kanawati975/Voron_Switchwire/Emergency Mount/Pictures/00.jpg

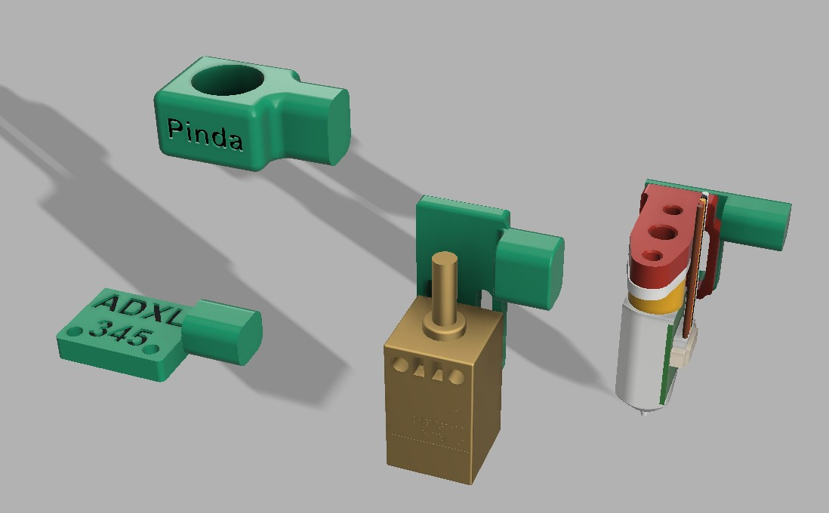
Emergency Mount/Pictures/00.jpg
