kanawati975/Voron_Switchwire/Emergency Mount/Pictures/1.jpg

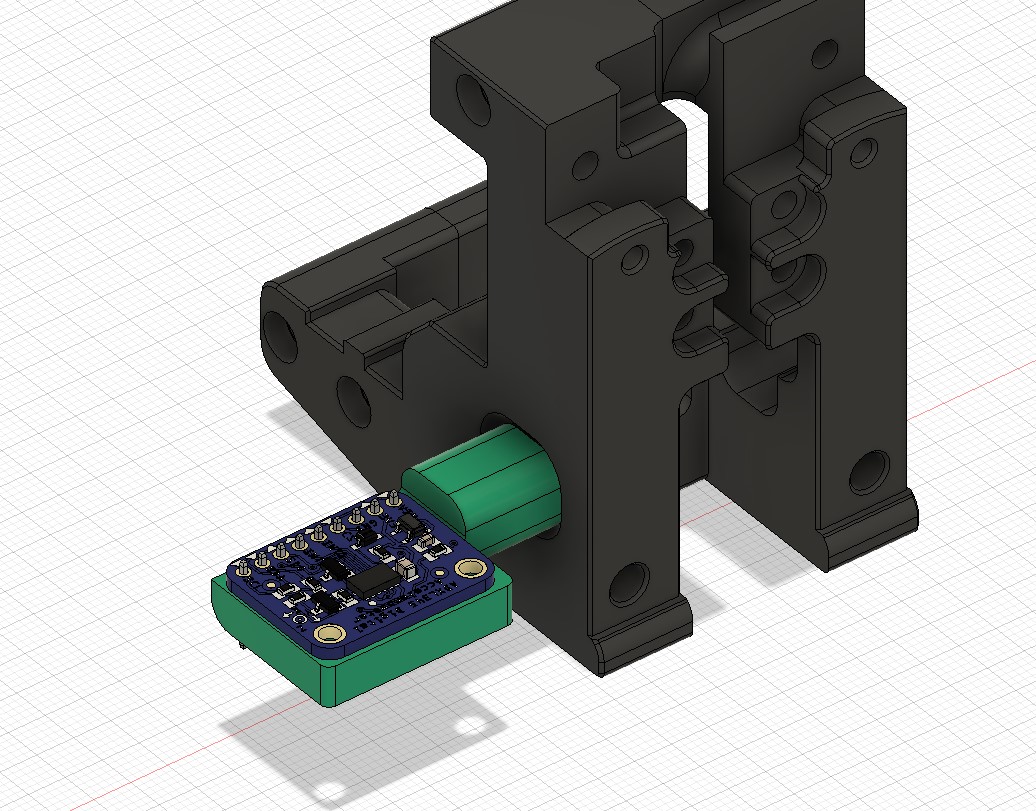
Emergency Mount/Pictures/1.jpg
