kanawati975/Voron_Switchwire/Emergency Mount/Pictures/2.jpeg

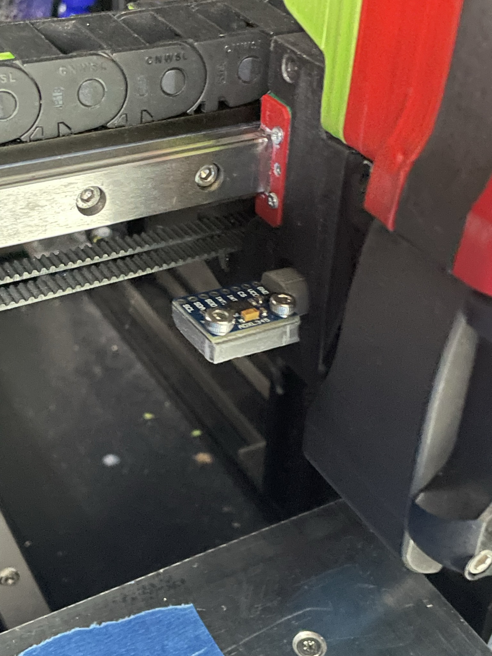
Emergency Mount/Pictures/2.jpeg
