kanawati975/Voron_Switchwire/Emergency Mount/Pictures/3.jpeg

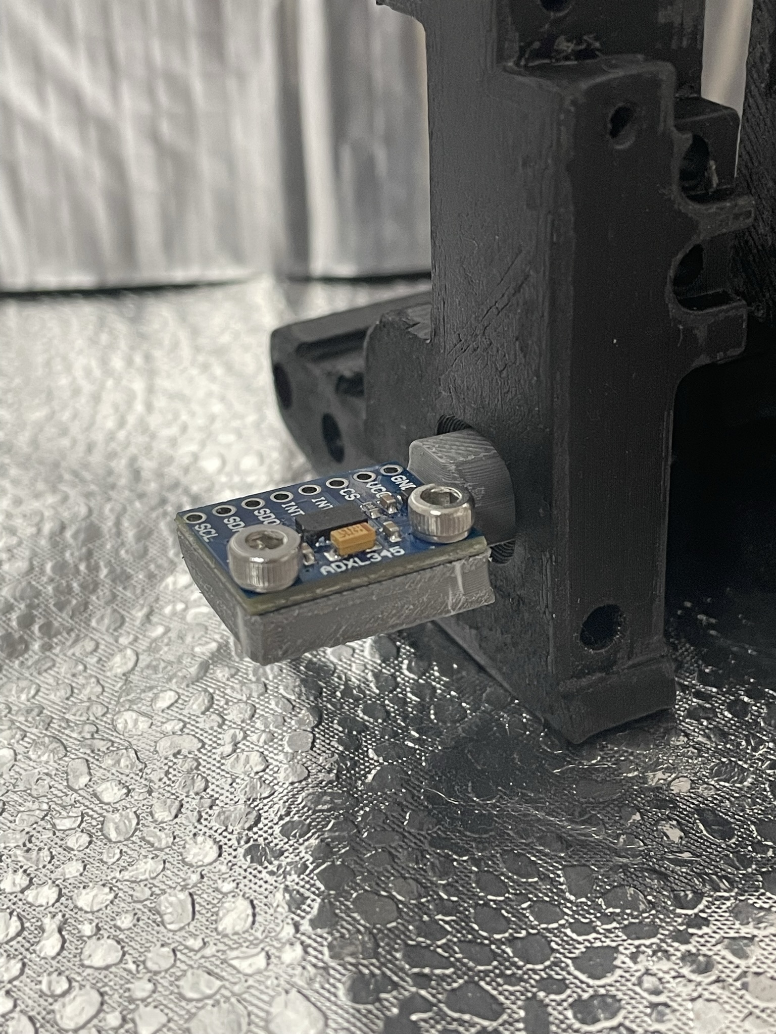
Emergency Mount/Pictures/3.jpeg
