kanawati975/Voron_Switchwire/Emergency Mount/Pictures/4.jpeg

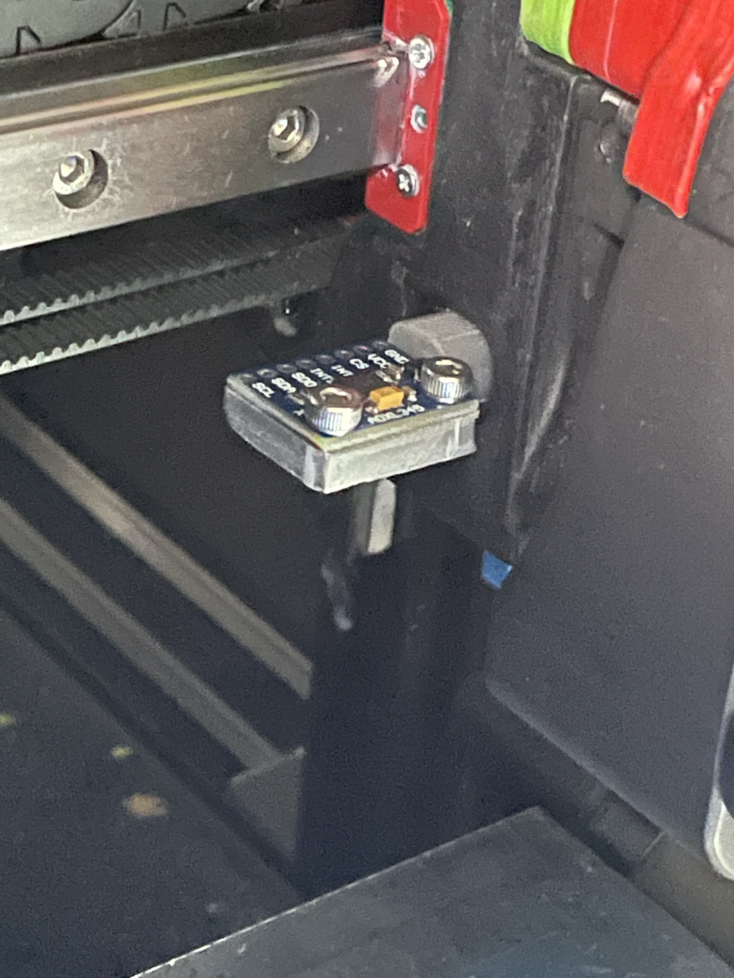
Emergency Mount/Pictures/4.jpeg
