kanawati975/Voron_Switchwire/Emergency Mount/Pictures/5.jpg

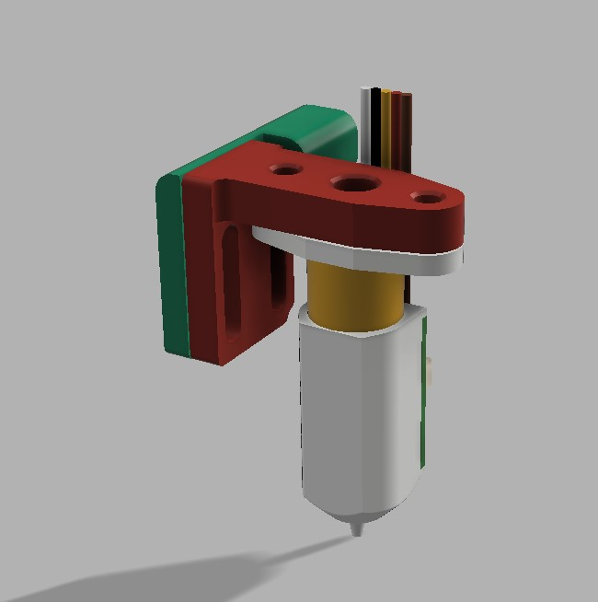
Emergency Mount/Pictures/5.jpg
