kanawati975/Voron_Switchwire/Emergency Mount/Pictures/6.jpeg

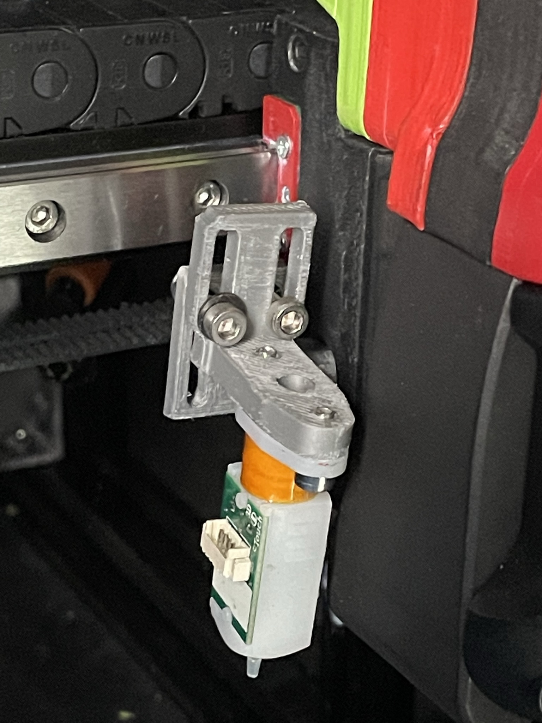
Emergency Mount/Pictures/6.jpeg
