kanawati975/Voron_Switchwire/Emergency Mount/Pictures/7.jpeg

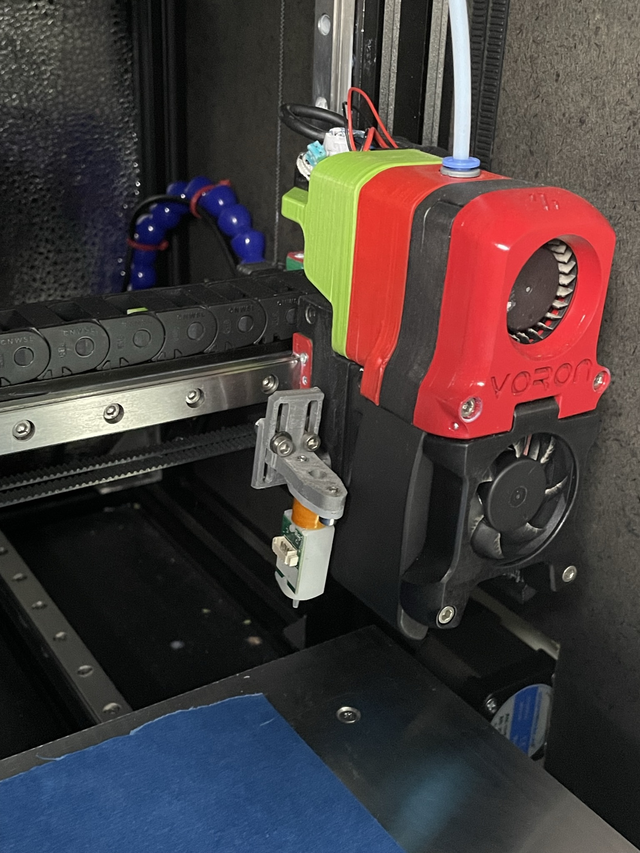
Emergency Mount/Pictures/7.jpeg
