kanawati975/Voron_Switchwire/Emergency Mount/Pictures/8.jpg

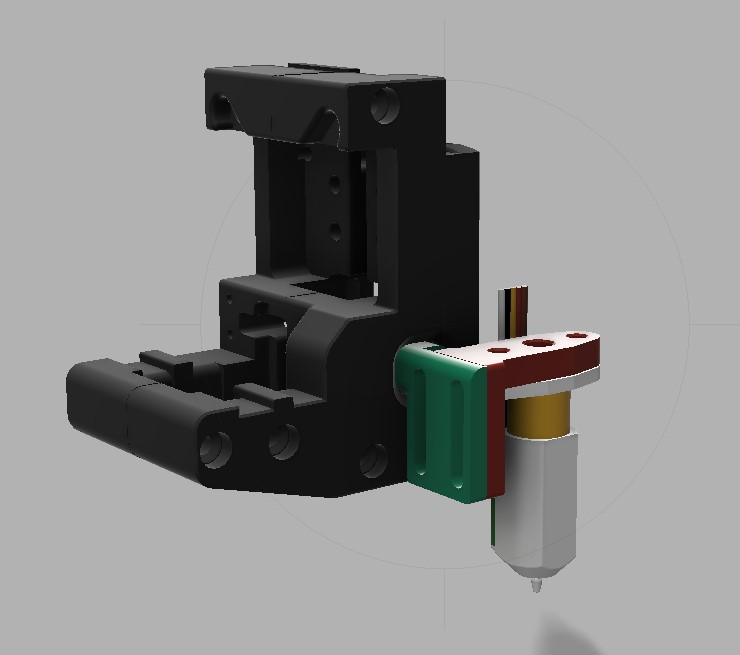
Emergency Mount/Pictures/8.jpg
