kanawati975/Voron_Switchwire/Emergency Mount/Pictures/9.jpg

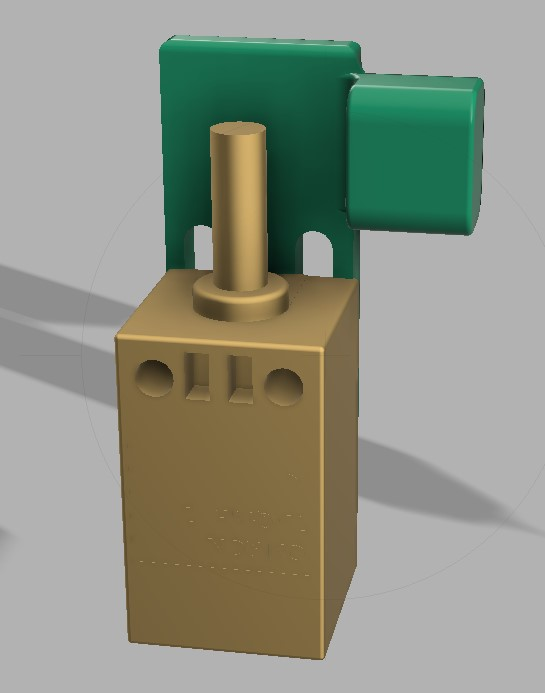
Emergency Mount/Pictures/9.jpg
