kanawati975/Voron_Switchwire/Images/IMG_6733.jpeg

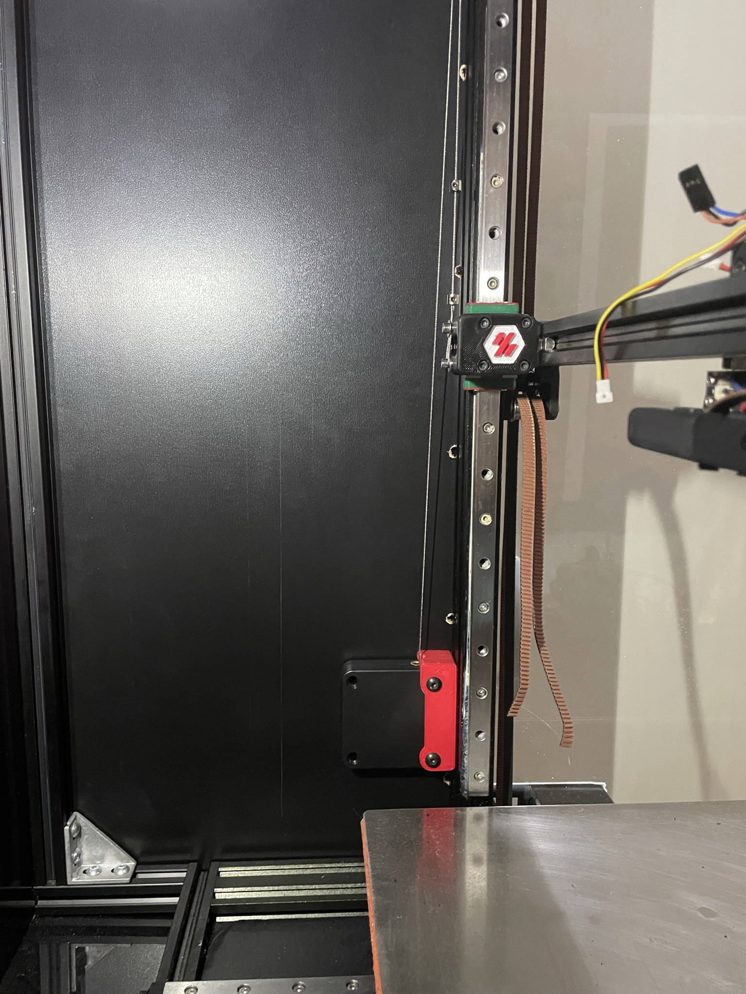
Images/IMG_6733.jpeg
