kanawati975/Voron_Switchwire/Images/IMG_6734.jpeg

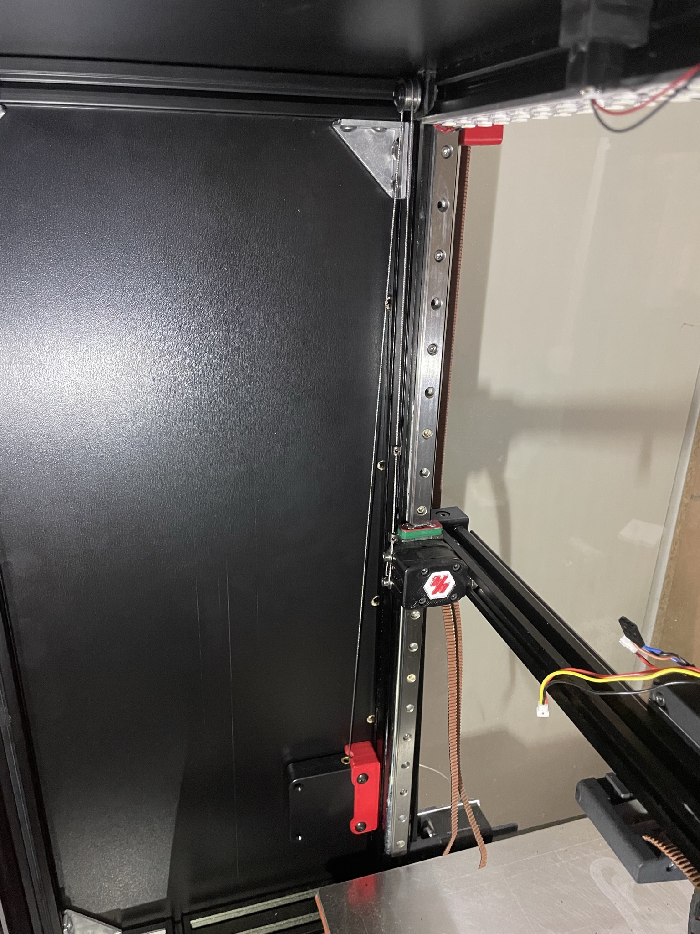
Images/IMG_6734.jpeg
