kanawati975/Voron_Switchwire/Images/IMG_6736.jpeg

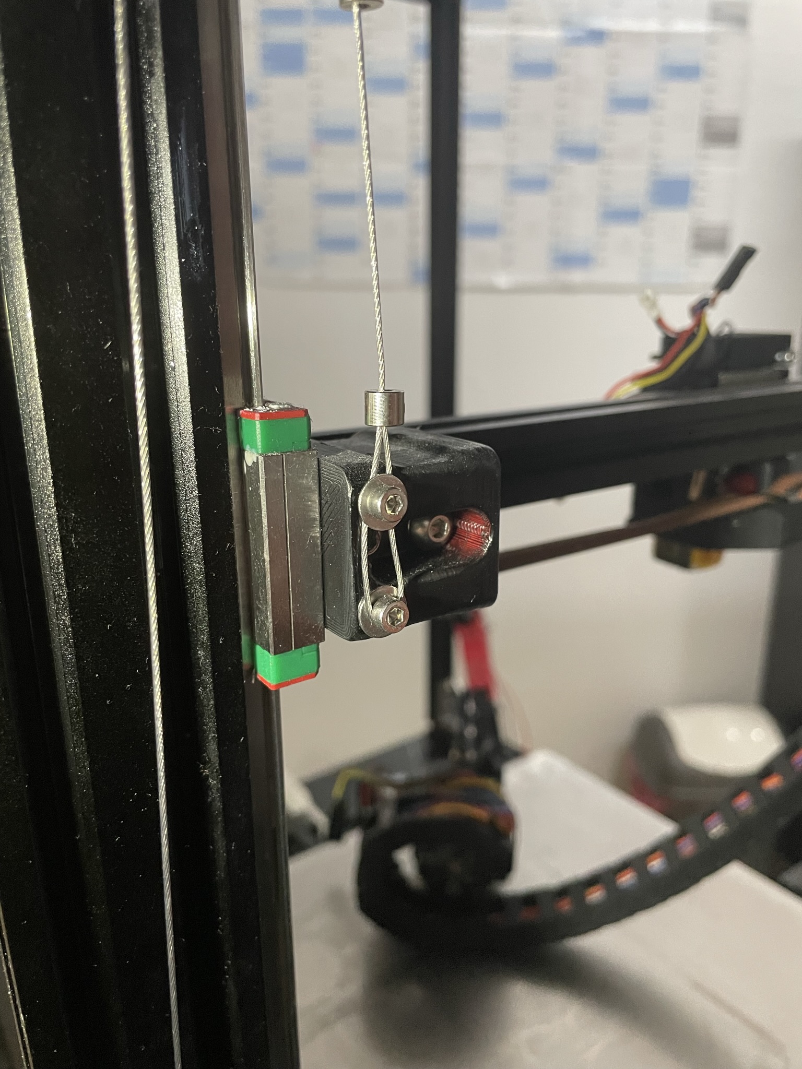
Images/IMG_6736.jpeg
