kanawati975/Voron_Switchwire/Images/IMG_6825.JPEG

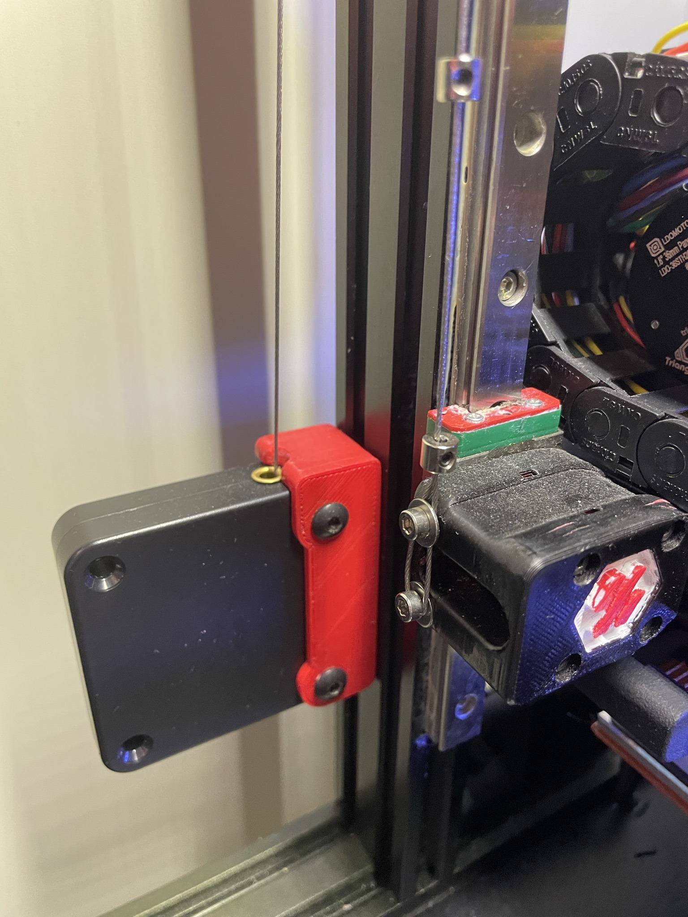
Images/IMG_6825.JPEG
