kanawati975/Voron_Switchwire/Images/IMG_6827.JPEG

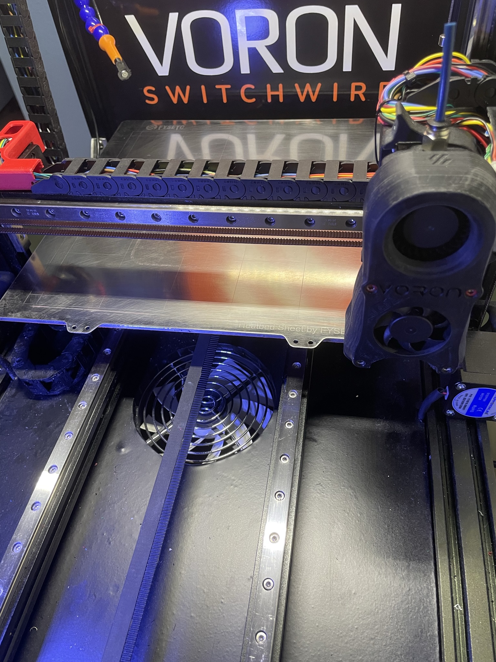
Images/IMG_6827.JPEG
