kanawati975/Voron_Switchwire/Images/IMG_6830.JPEG

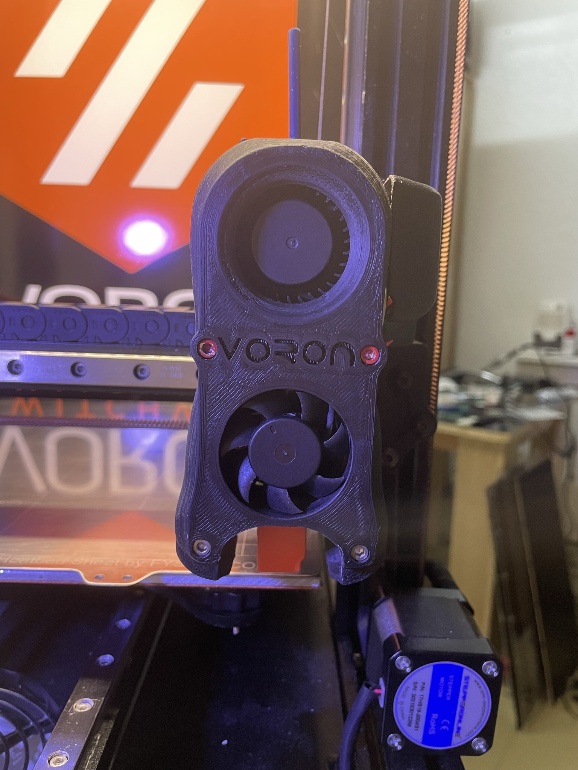
Images/IMG_6830.JPEG
