kanawati975/Voron_Switchwire/Images/IMG_6831.JPEG

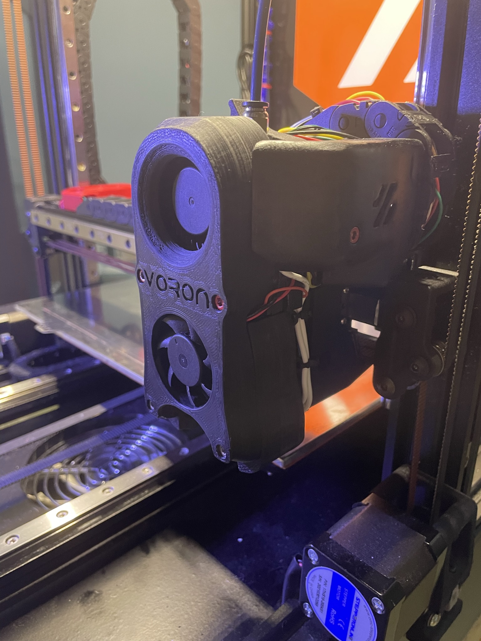
Images/IMG_6831.JPEG
