kanawati975/Voron_Switchwire/Images/IMG_6832.JPEG

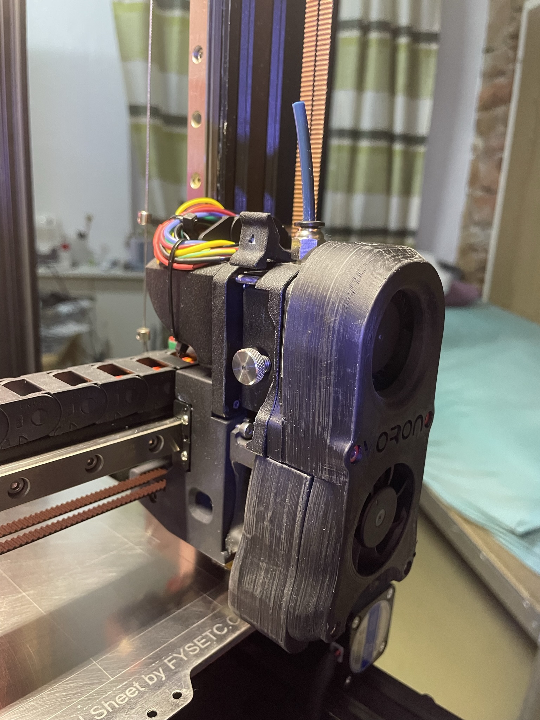
Images/IMG_6832.JPEG
