kanawati975/Voron_Switchwire/Images/IMG_6833.JPEG

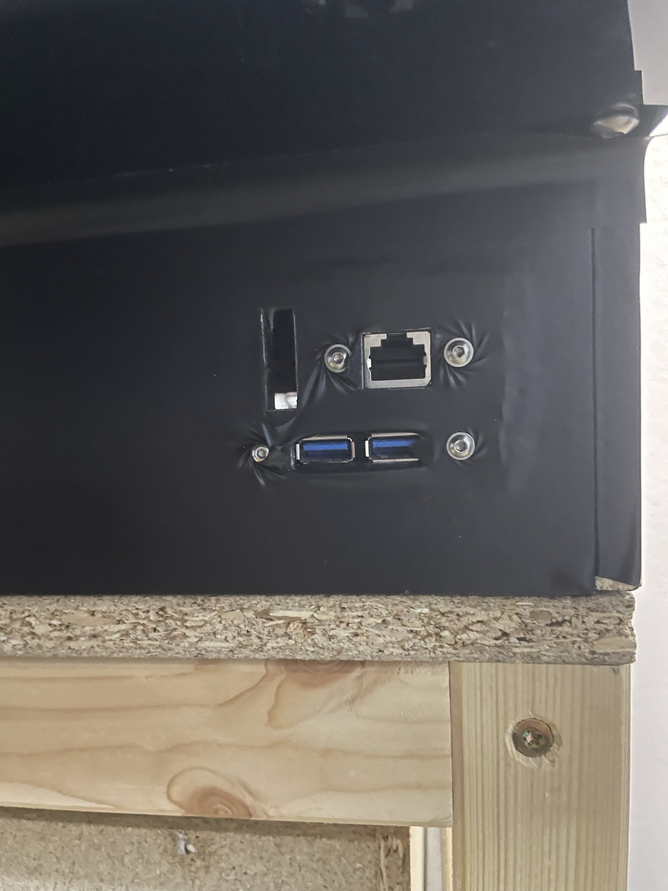
Images/IMG_6833.JPEG
