kanawati975/Voron_Switchwire/Images/IMG_6835.JPEG

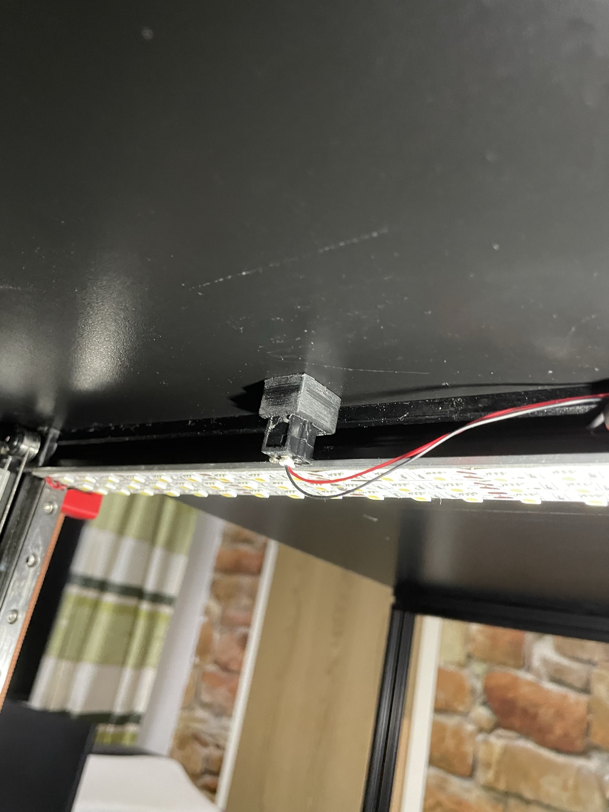
Images/IMG_6835.JPEG
