kanawati975/Voron_Switchwire/Images/IMG_6837.JPEG

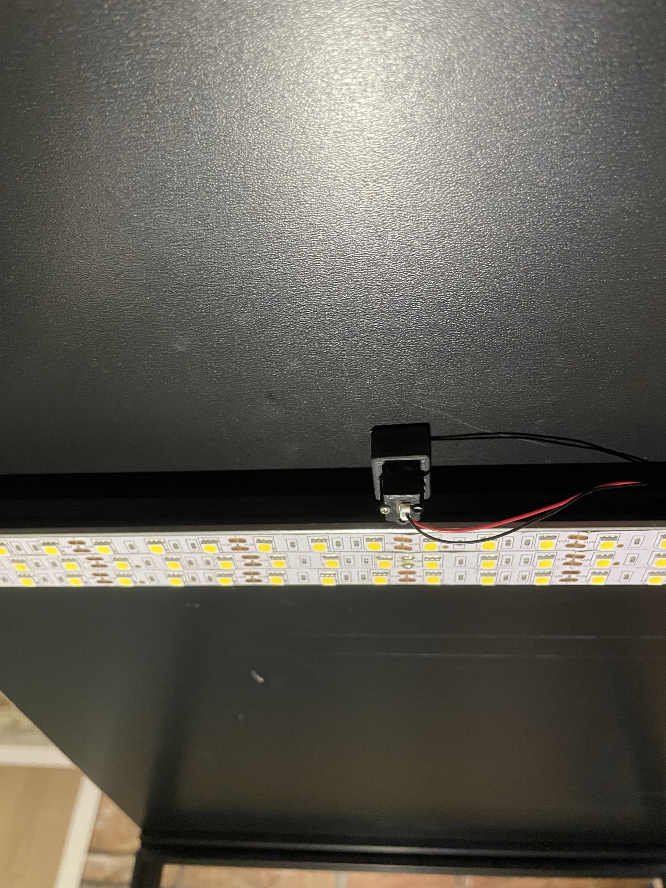
Images/IMG_6837.JPEG
