kanawati975/Voron_Switchwire/Images/IMG_6838.JPEG

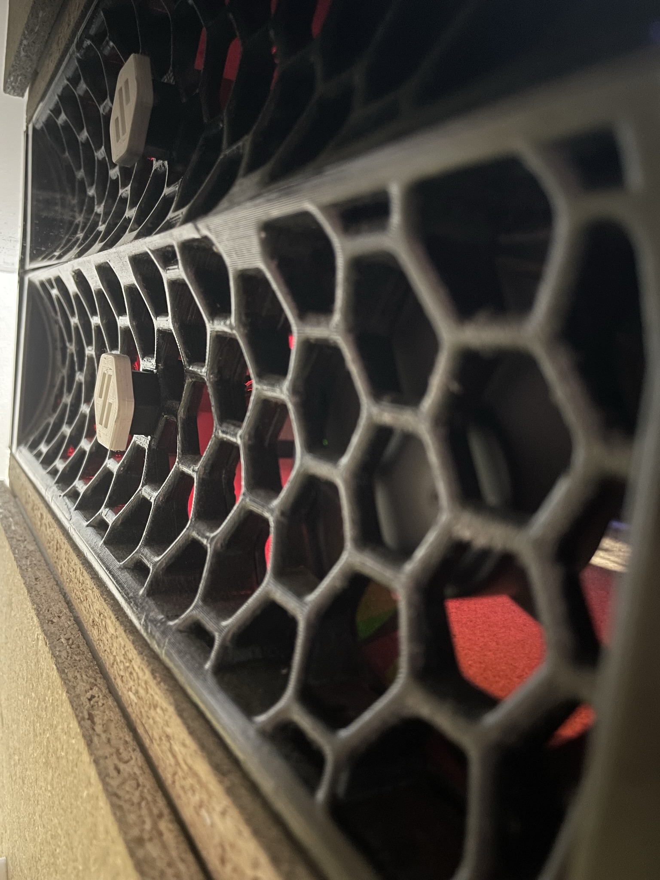
Images/IMG_6838.JPEG
