kanawati975/Voron_Switchwire/Images/IMG_6839.JPEG

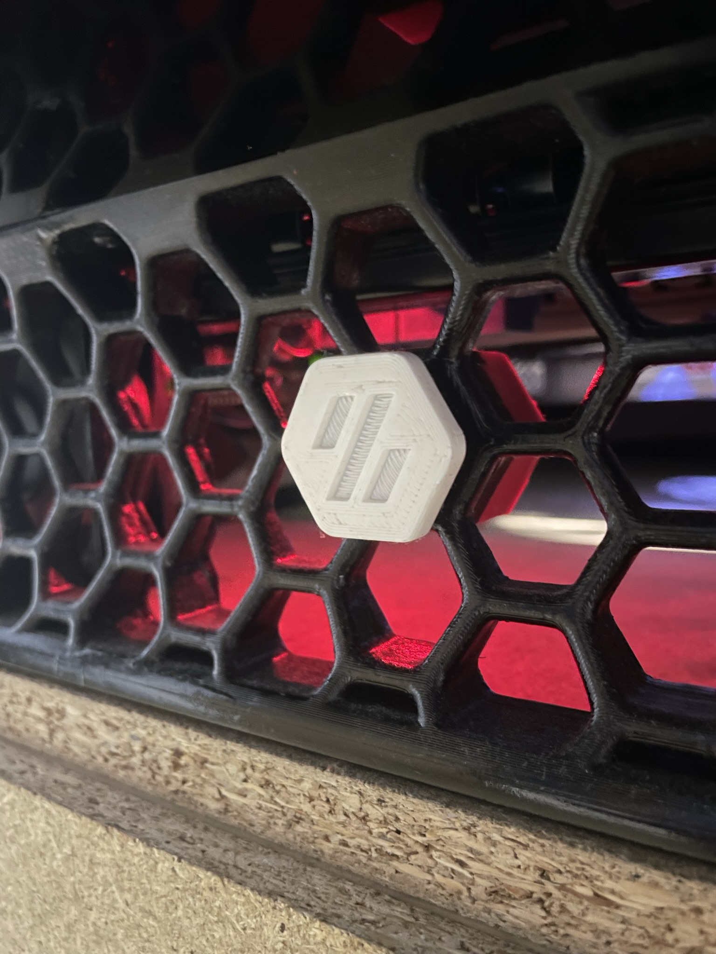
Images/IMG_6839.JPEG
