kanawati975/Voron_Switchwire/Images/Screenshot 2022-02-22 232121.jpg

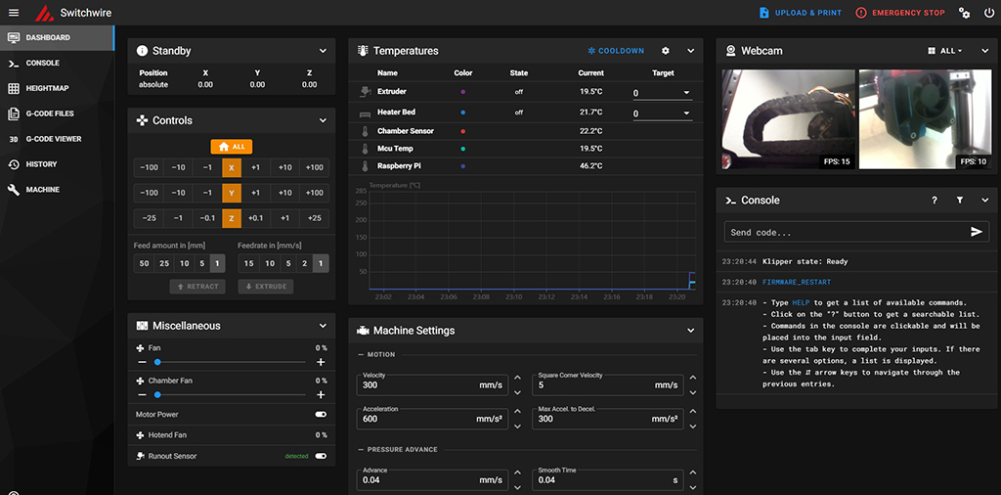
Images/Screenshot 2022-02-22 232121.jpg
