kanawati975/Voron_Switchwire/Images/Screenshot 2022-02-26 214539.jpg

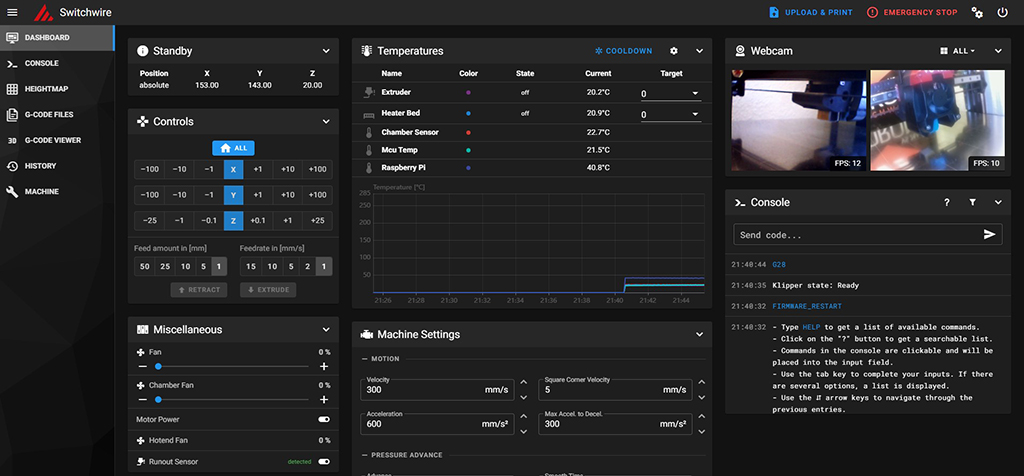
Images/Screenshot 2022-02-26 214539.jpg
