kanawati975/Voron_Switchwire/Key-Bak/Key-Bak_Alternative_1.jpg

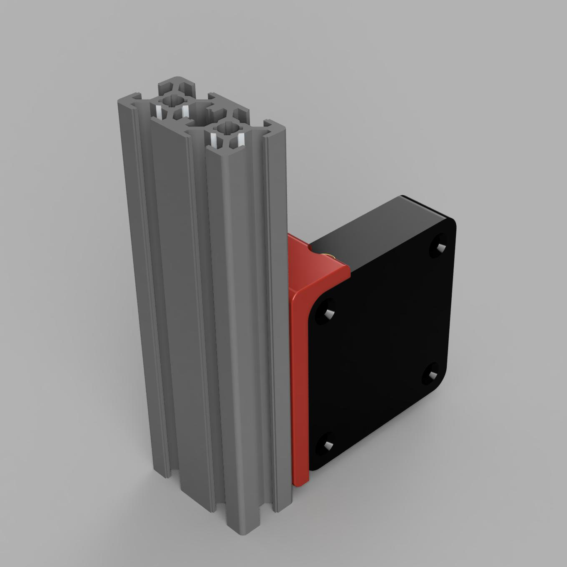
Key-Bak/Key-Bak_Alternative_1.jpg
