kanawati975/Voron_Switchwire/Key-Bak/Key-Bak_Alternative_2.JPEG

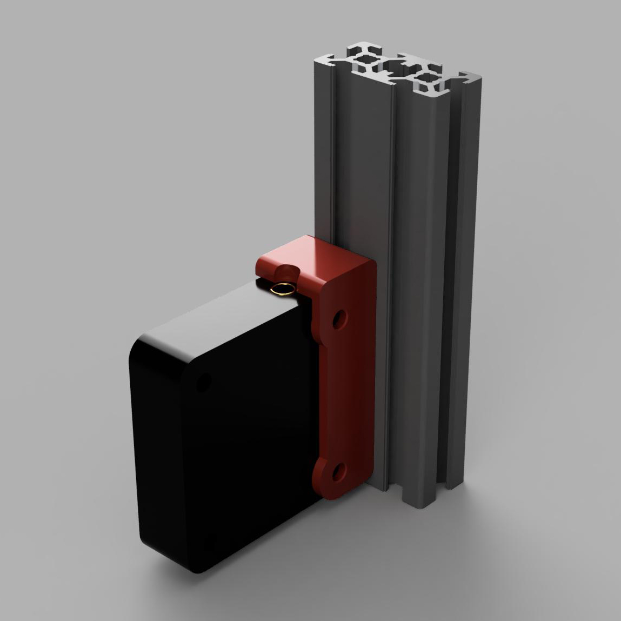
Key-Bak/Key-Bak_Alternative_2.JPEG
