kanawati975/Voron_Switchwire/Volcano_Toolhead/IMG_4371.jpeg

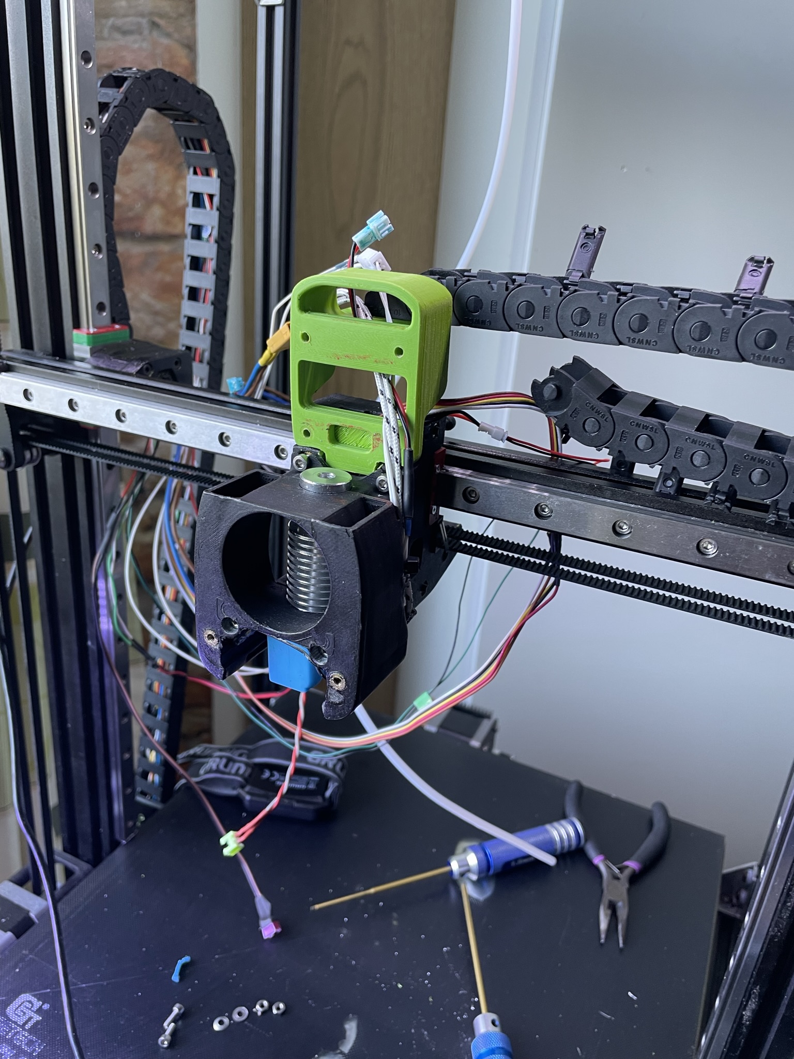
Volcano_Toolhead/IMG_4371.jpeg
