kanawati975/Voron_Switchwire/Volcano_Toolhead/Screenshot 2021-11-01 054901.jpg

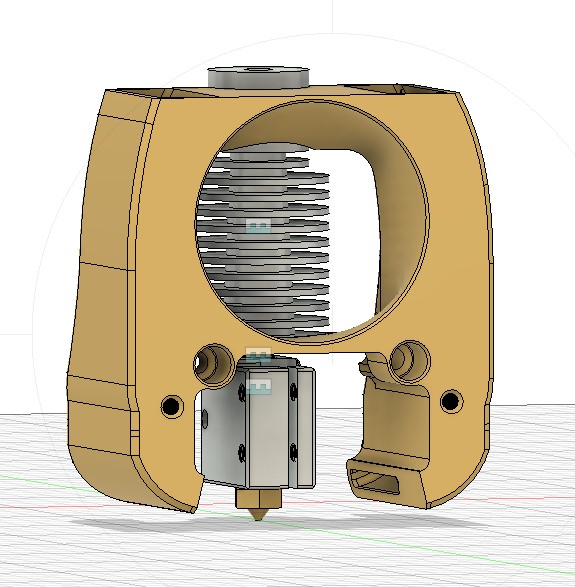
Volcano_Toolhead/Screenshot 2021-11-01 054901.jpg
