kanawati975/Voron_Switchwire/VSW.jpg

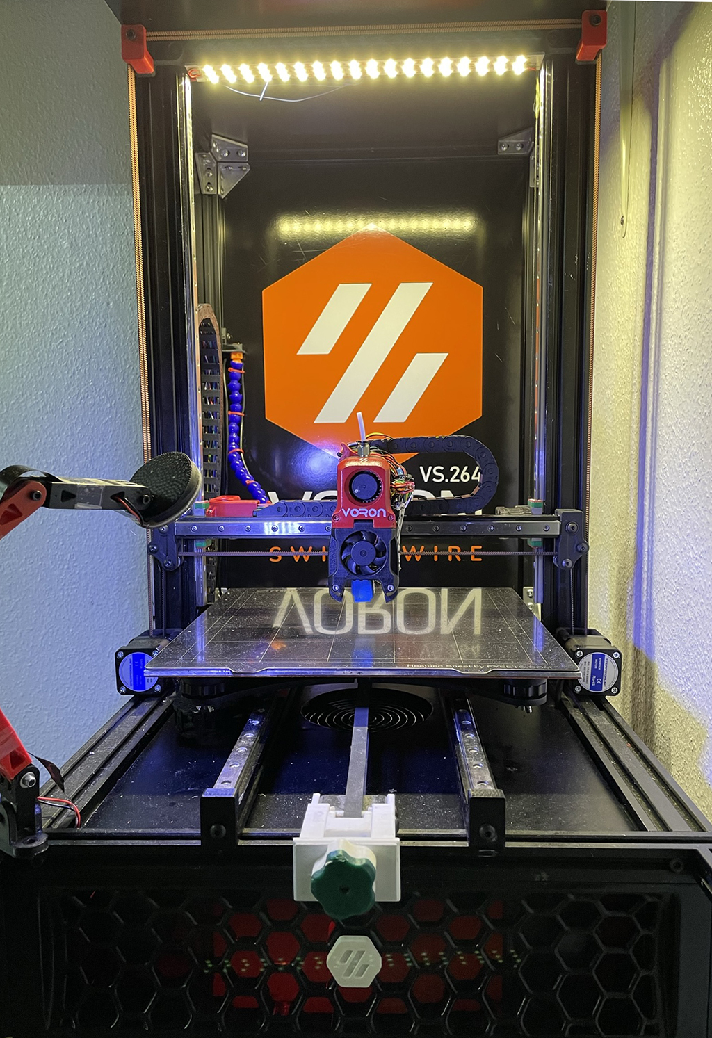
VSW.jpg
