kanawati975/Voron_Switchwire/Motor Mount/X_motor_mount_a.stl

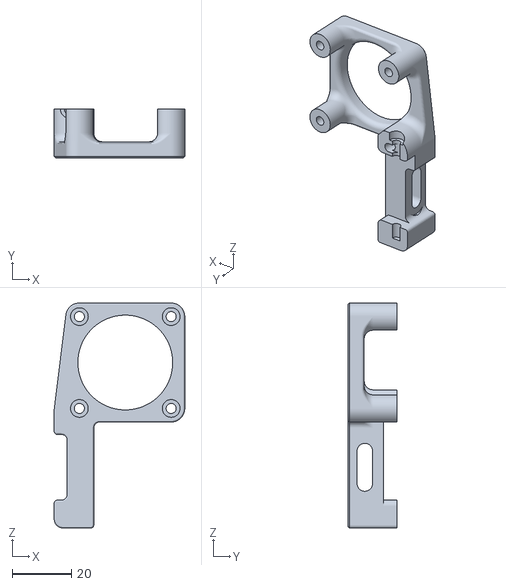
[picture p66: CAD file, 2022-09-13]
Motor Mount/X_motor_mount_a.stl
44.1 x 16.4 x 76.0
