kanawati975/Voron_Switchwire/Pi-Cam/Joint00.stl

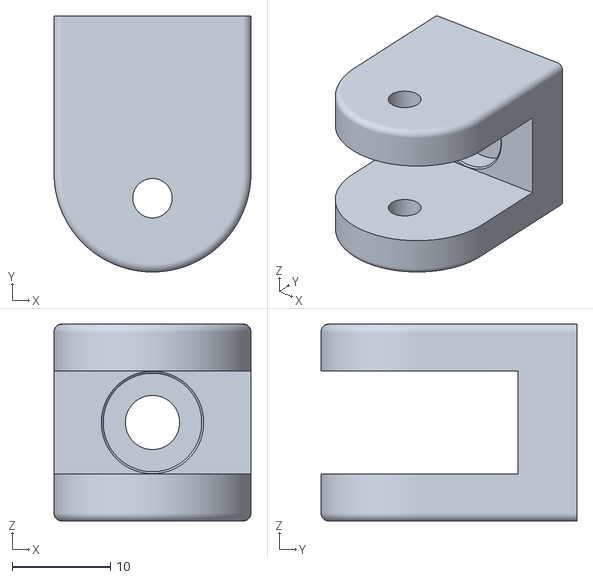
[picture p67: CAD file, 2021-11-01]
Pi-Cam/Joint00.stl
20.0 x 26.0 x 20.0
