kanawati975/Voron_Switchwire/XY_Gantry_Blocks/xz_block_left_a.stl

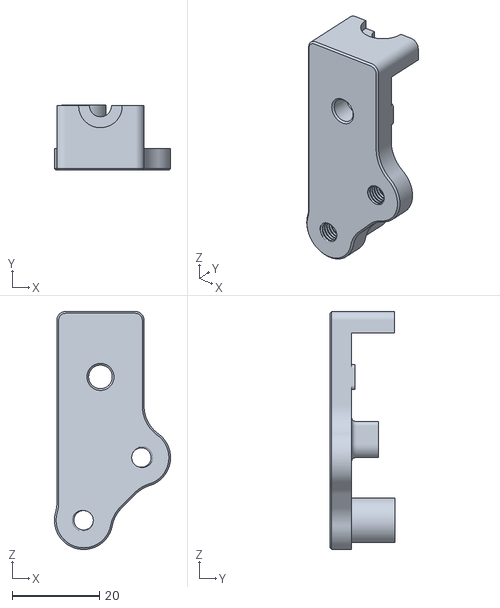
[picture p68: CAD file, 2022-05-08]
XY_Gantry_Blocks/xz_block_left_a.stl
26.6 x 15.0 x 54.6
