kanawati975/Voron_Switchwire/Emergency Mount/STL/Bltouch.stl

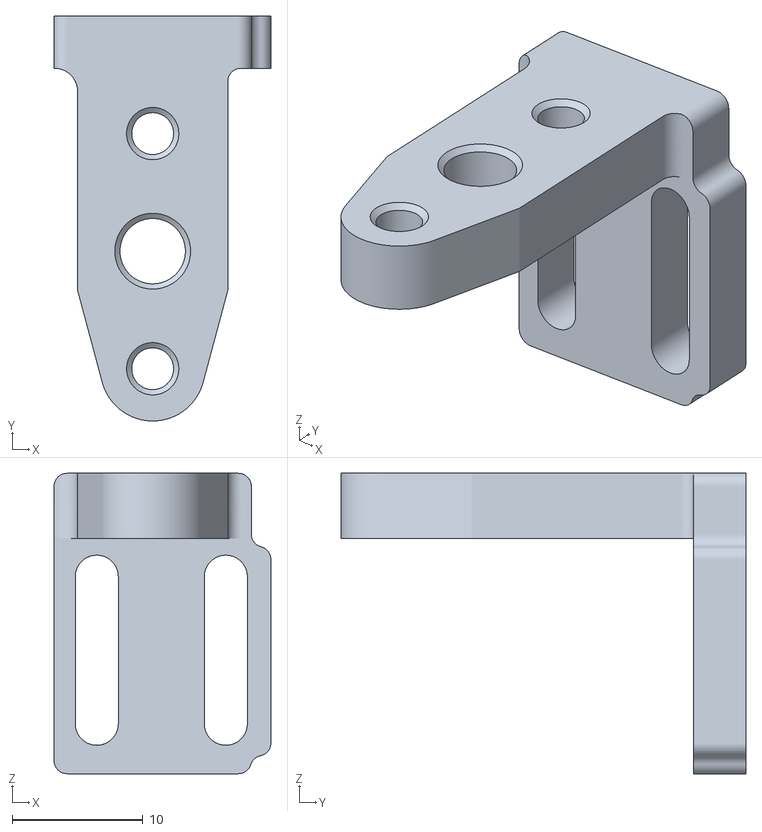
[picture p69: CAD file, 2021-11-28]
Emergency Mount/STL/Bltouch.stl
16.6 x 31.0 x 23.0
