kanawati975/Voron_Switchwire/Pi-Cam/90deg_Adapter.stl

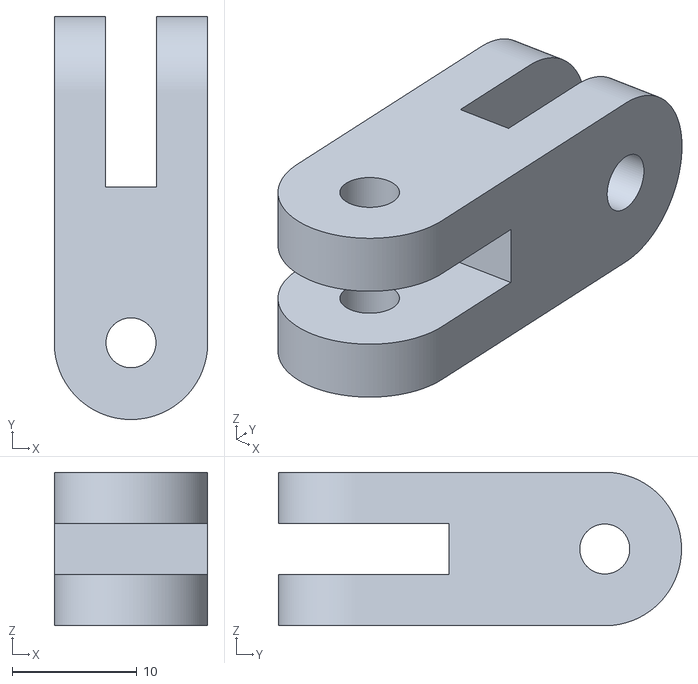
[picture p71: CAD file, 2021-11-01]
Pi-Cam/90deg_Adapter.stl
12.3 x 32.3 x 12.3
