kanawati975/Voron_Switchwire/Upper_XZ_Blocks/XZ_Block_Left.stl

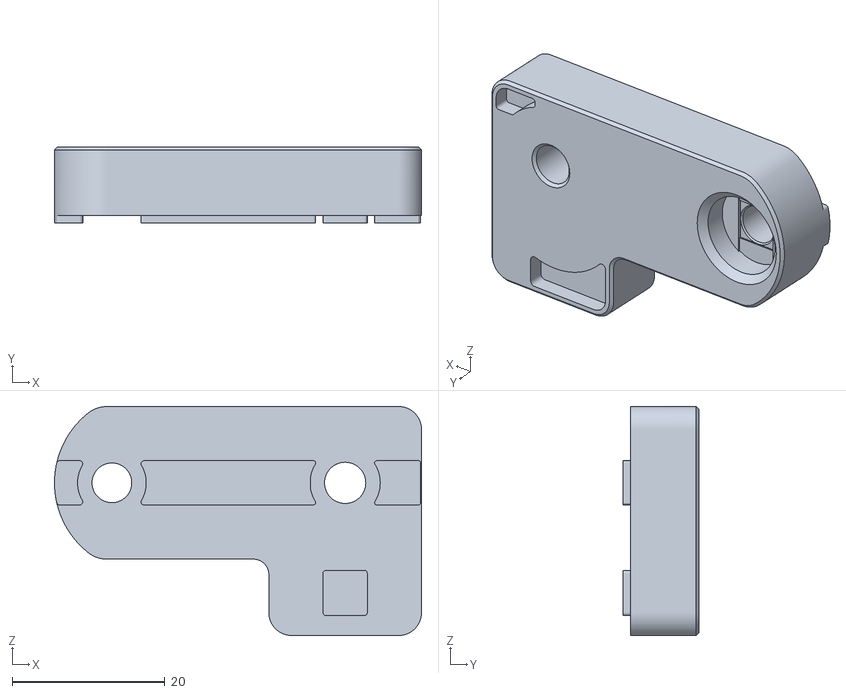
[picture p72: CAD file, 2022-05-08]
Upper_XZ_Blocks/XZ_Block_Left.stl
48.1 x 10.0 x 30.0
