kanawati975/Voron_Switchwire/Emergency Mount/STL/ADXL345_Mount.stl

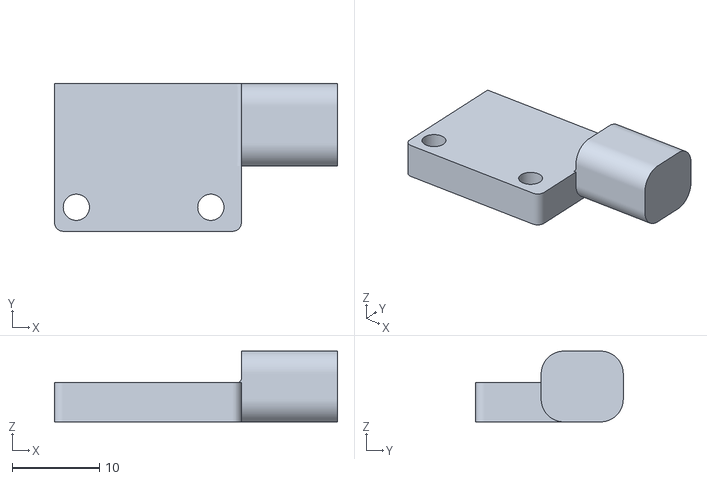
[picture p73: CAD file, 2021-11-28]
Emergency Mount/STL/ADXL345_Mount.stl
32.4 x 16.9 x 8.10
