kanawati975/Voron_Switchwire/Pi-Cam/4xLink.stl

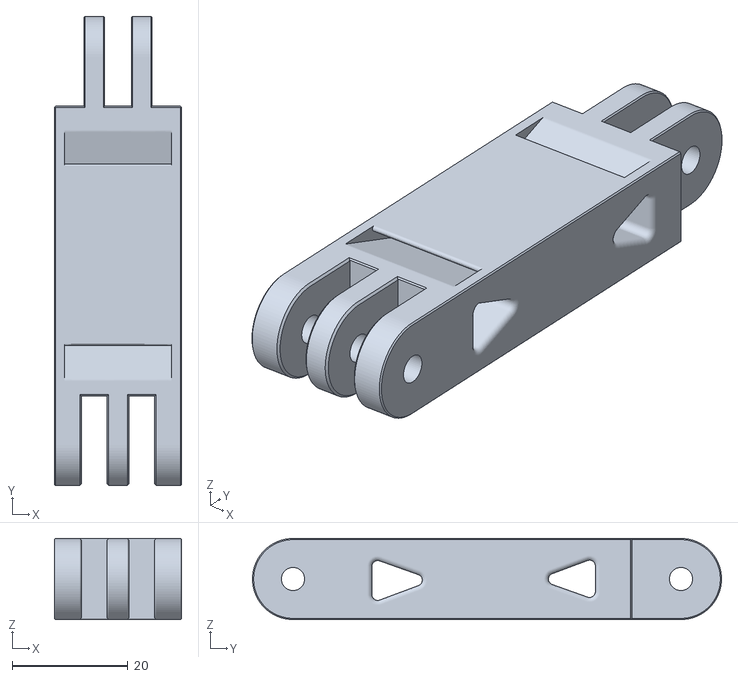
[picture p74: CAD file, 2021-11-01]
Pi-Cam/4xLink.stl
22.0 x 81.0 x 14.0
