kanawati975/Voron_Switchwire/Pi-Cam/Cam_Mount.stl

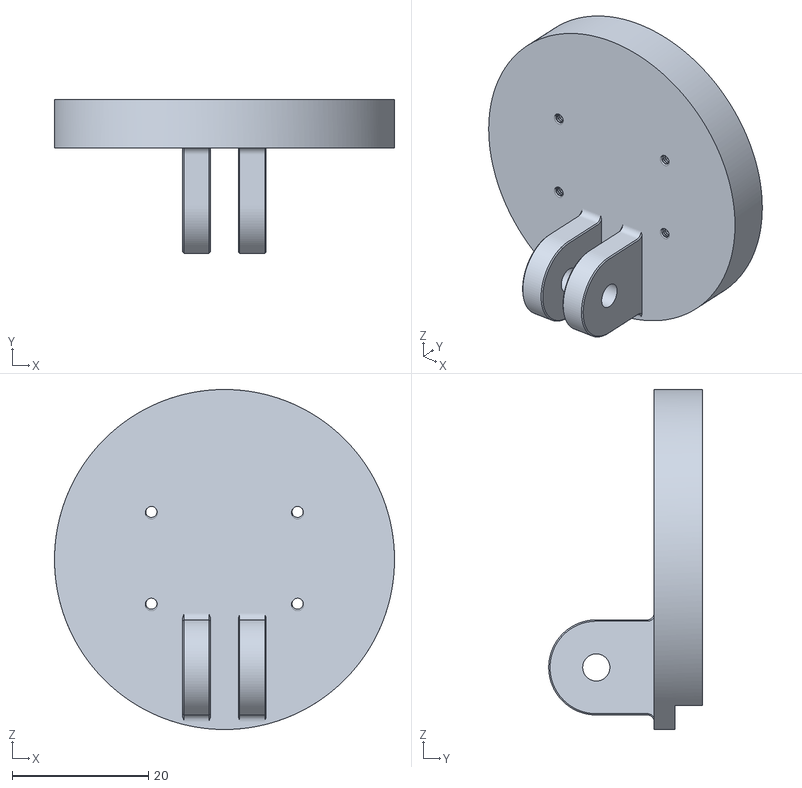
[picture p75: CAD file, 2021-11-01]
Pi-Cam/Cam_Mount.stl
50.0 x 22.6 x 50.0
